ansonl/FordACP-AUX/Resources/Ford Bluetooth Interface V1.0 - Dale Thomas/Misc Documents/Misc Documents/Misc Documents/Radio Connectors/Connectors/174051-2/3D_CVM_CVM_174051-2_K.pdf

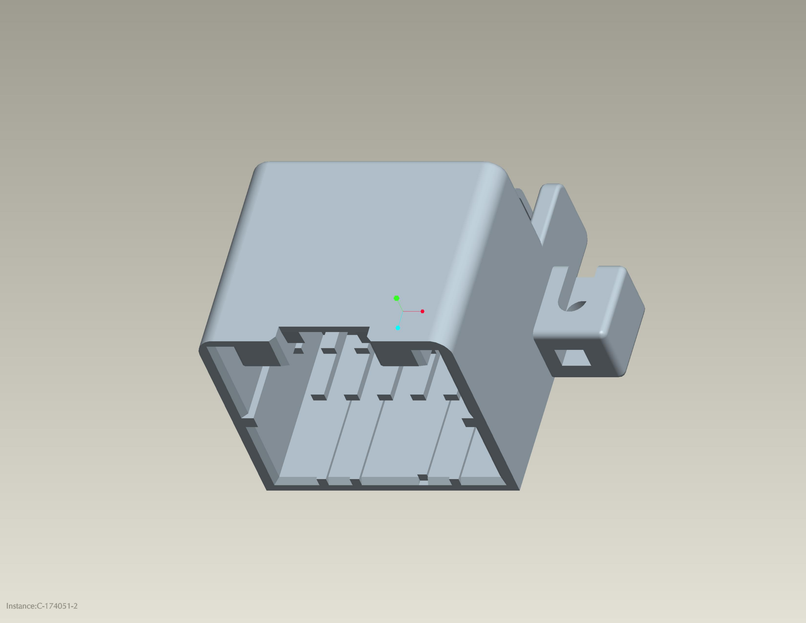
[picture p7: page 1]
