ansonl/FordACP-AUX/Resources/Ford Bluetooth Interface V1.0 - Dale Thomas/Misc Documents/Misc Documents/Misc Documents/Radio Connectors/Connectors/175180-1/JPN_CD_175180_B4_CD_175180 (1).pdf

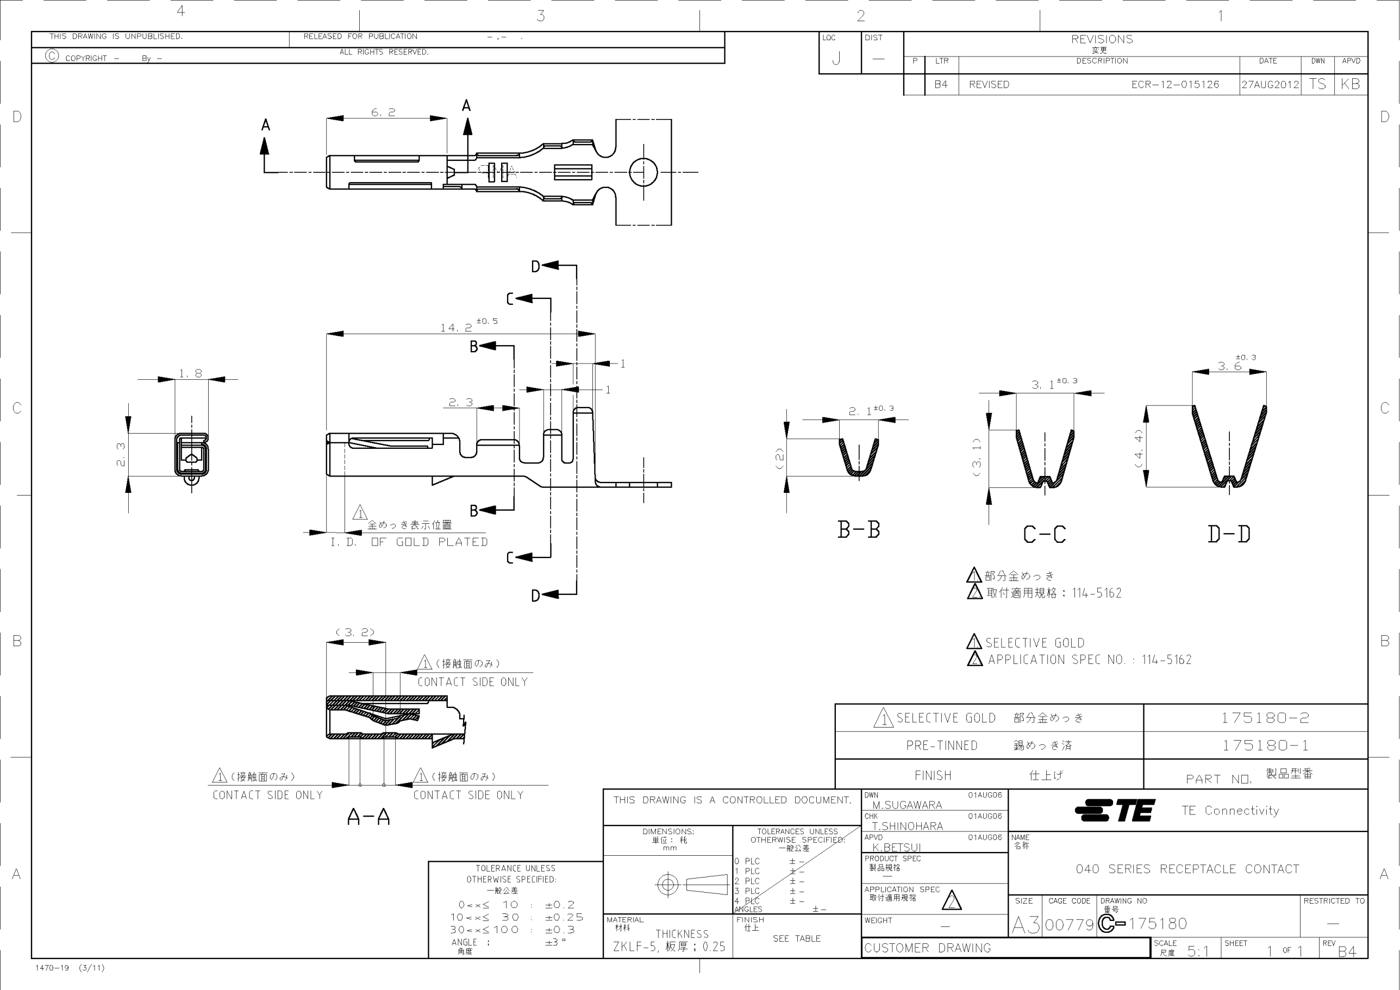
[picture p8: page 1]
