ansonl/FordACP-AUX/Resources/Ford Bluetooth Interface V1.0 - Dale Thomas/Misc Documents/Misc Documents/Misc Documents/ACP/FORDs_ACP_Protocol/page05.bmp

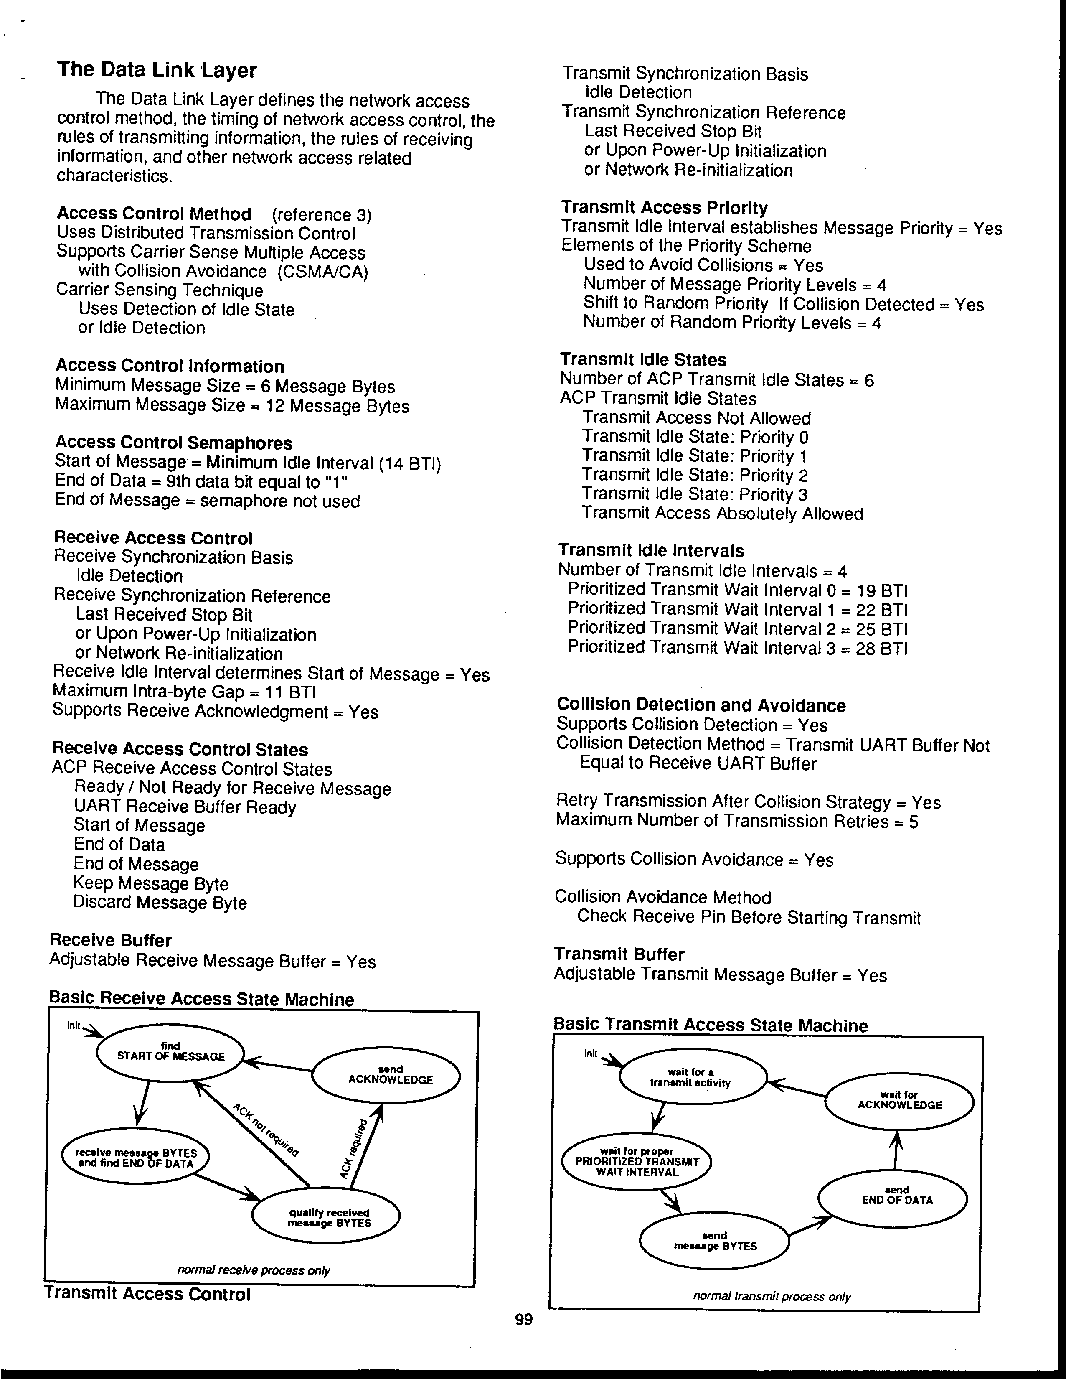
Resources/Ford Bluetooth Interface V1.0 - Dale Thomas/Misc Documents/Misc Documents/Misc Documents/ACP/FORDs_ACP_Protocol/page05.bmp
