ansonl/FordACP-AUX/Resources/Ford Bluetooth Interface V1.0 - Dale Thomas/Misc Documents/Misc Documents/Misc Documents/Radio Connectors/Connectors/174051-2/ENG_CD_174051_J7.pdf

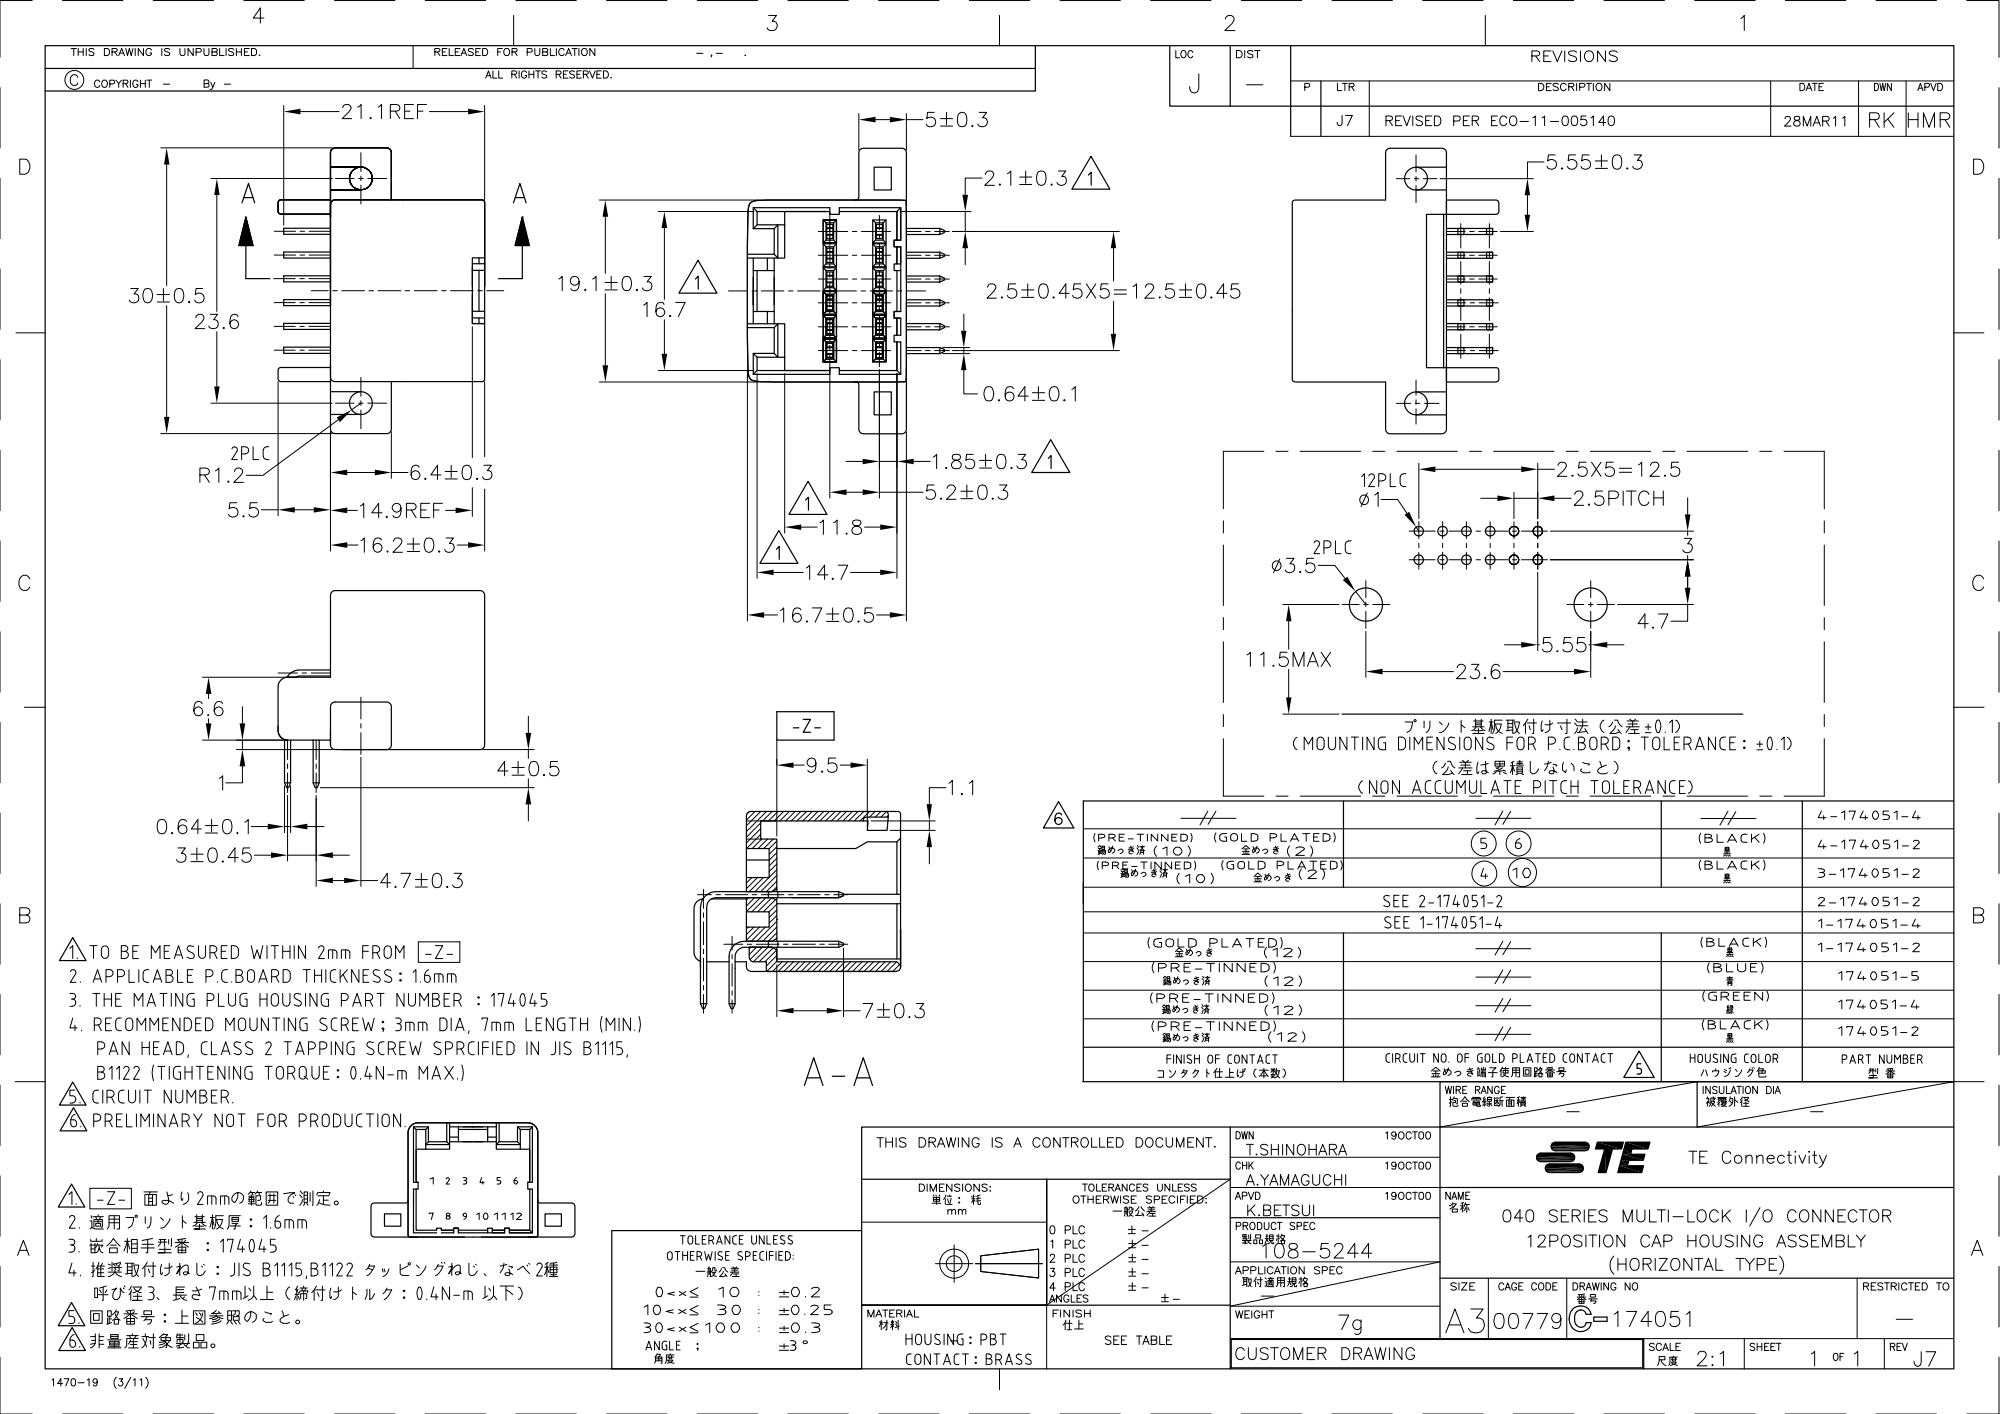
[picture p36: page 1]
